atsidaev/4116_DRAM_Tester/hardware/hardware.kicad_sch

## KiCad design hardware/hardware.kicad_sch (2026-03-15)

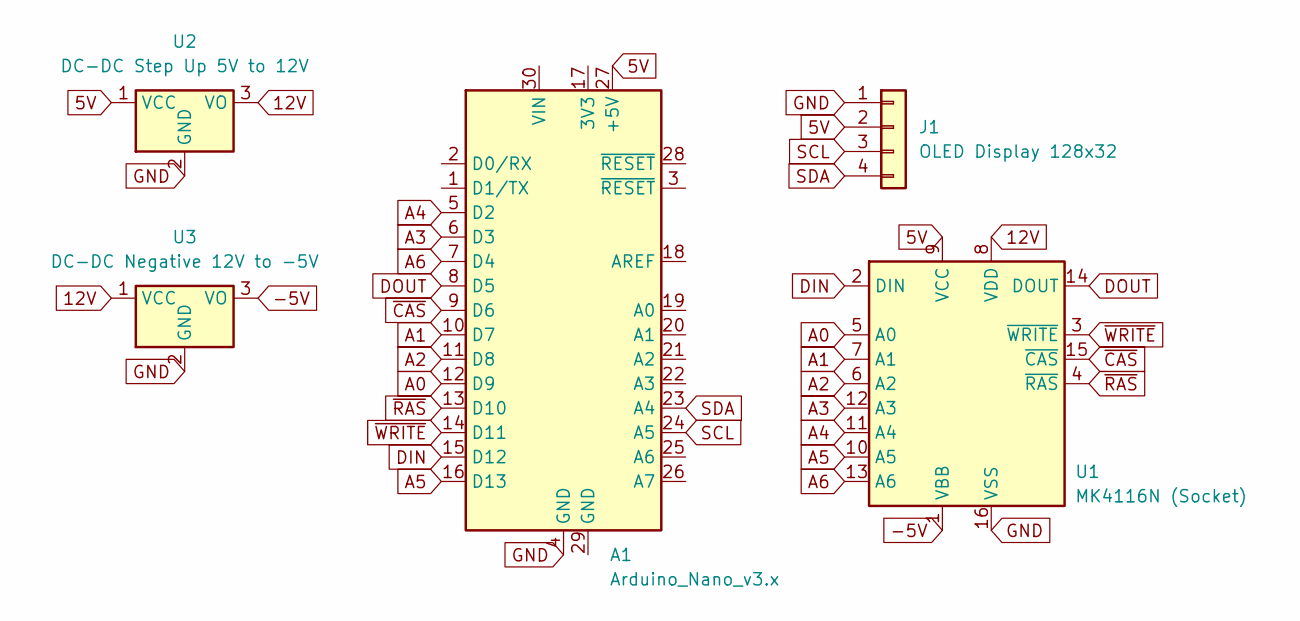
[picture p3: schematic hardware.kicad_sch]

Parts:
A1: Arduino_Nano_v3.x; Arduino_Nano
J1: OLED Display 128x32
U1: MK4116N (Socket); DIP-16_W7.62mm
U2: DC-DC Step Up 5V to 12V; TO-252-2
U3: DC-DC Negative 12V to -5V; TO-252-2

Connections:
5V: A1.27 (+5V), J1.2, U1.9 (VCC), U2.1 (VCC)
12V: U1.8 (VDD), U2.3 (VO), U3.1 (VCC)
-5V: U1.1 (VBB), U3.3 (VO)
A0: A1.12 (D9), U1.5 (A0)
A1: A1.10 (D7), U1.7 (A1)
A2: A1.11 (D8), U1.6 (A2)
A3: A1.6 (D3), U1.12 (A3)
A4: A1.5 (D2), U1.11 (A4)
A5: A1.16 (D13), U1.10 (A5)
A6: A1.7 (D4), U1.13 (A6)
DIN: A1.15 (D12), U1.2 (DIN)
DOUT: A1.8 (D5), U1.14 (DOUT)
GND: A1.4 (GND), J1.1, U1.16 (VSS), U2.2 (GND), U3.2 (GND)
SCL: A1.24 (A5), J1.3
SDA: A1.23 (A4), J1.4
~CAS: A1.9 (D6), U1.15 (~CAS)
~RAS: A1.13 (D10), U1.4 (~RAS)
~WRITE: A1.14 (D11), U1.3 (~WRITE)
