atsidaev/4116_DRAM_Tester/firmware/pinout.h

#ifndef __PINOUT_H
#define __PINOUT_H

// 4116 PINOUT

#define XA0    DIP_05
#define XA1    DIP_07
#define XA2    DIP_06
#define XA3    DIP_12
#define XA4    DIP_11
#define XA5    DIP_10
#define XA6    DIP_13

#define DI     DIP_02
#define DO     DIP_14

#define nCAS   DIP_15
#define nRAS   DIP_04
#define nWRITE DIP_03

// DIP-16 Socket wiring to Arduino pins

#define DIP_01 "-5"
#define DIP_02 12
#define DIP_03 11
#define DIP_04 10
#define DIP_05 9
#define DIP_06 8
#define DIP_07 7
#define DIP_08 "+12"
#define DIP_09 "+5"
#define DIP_10 13
#define DIP_11 2
#define DIP_12 3
#define DIP_13 4
#define DIP_14 5
#define DIP_15 6
#define DIP_16 "GND"

#define LED 13

#endif
